jonaheinke/dac/spice/test/Draft1.asc

C1: cap; 3µ3
C2: cap; 22µ
C3: cap; 3µ3
C4: cap; 220µ
Q1: pnp
Q2: npn
Q3: pnp
Q4: pnp
Q5: npn
Q6: npn
Q7: npn
R1: res; 2k2
R2: res; 10k
R3: res; 10k
R4: res; 22k
R5: res; 22k
R6: res; 100
R7: res; 9k
R8: res; 1k
R9: res; 100k
R10: res; 5R6
R11: res; 10k
R12: res; 250
V1: voltage; SINE(0 250m 1k)
V2: voltage; 11; Rser=100k
V3: voltage; 22
Named nets: 0
