jonaheinke/dac/spice/test/Example_BJT_THD_TEST.asc

C1: cap; 1µ
C2: cap; 330µ
J1: njf; BF862
M2: nmos; ZVN4306A
R1: res; 100k
R2: res; 47k
R3: res; 68
R4: res; 470
R5: res; 68
R6: res; 2k
R7: res; 250
R8: res; 68
V1: voltage; 22
V2: voltage; SINE(0 250m 1k)
Named nets: 0, out
;.inc Analyzer_Controls.txt
;.tran 0 {AnalysisTime} {SettlingTime} {MaxTimestep}
.inc BF862.sub
.inc ZVN4306.sub
.tran 0 100m 0 1u
.four 1k V(out)
.option numdgt=7
;.inc ZXMN10A08E6.sub
;.inc 2SK209GR.txt
.model 2SK209BL NJF vto = -0.7869
+ beta = 0.021 lambda = 6.15e-3 rd = 12.194
+ rs = 16.746 is = 2.613e-15 cgd = 1.458e-11
+ cgs = 1.478e-11 pb = 0.3754
+ fc = 0.5 N = 1
;.op
.options plotwinsize=0
