jonaheinke/dac/spice/current_source.asc

Q1: pnp; 2N4126
Q2: pnp; 2N4126
R1: res; 150
R2: res; 33k
R3: res; 800
V2: voltage; SINE(20 1 20k); Rser=10
Named nets: 0, input, output
;.step dec param R 1 100k 100
;.op
;.tran 0 30 0 0.1
;.step param V 1 12 1
.tran 0 0.5m 0 10n
