jonaheinke/dac/spice/DC_detection_2.asc

C1: cap; 10µ
C2: cap; 10µ
C3: cap; 2µ2
D1: diode; 1N914
D2: diode; 1N914
D3: diode; 1N914
D4: diode; 1N914
Q2: pnp
Q3: pnp
Q4: npn
Q5: npn
R1: res; 100k
R2: res; 100k
R3: res; 10k
R4: res; 100k
R5: res; 100k
R6: res; 2k5
R7: res; 22k
R8: res; 22k
R9: res; 47k
R10: res; 2k2
R11: res; 100k
R12: res; 100k
V1: voltage; 24; Rser=2
V3: voltage; SINE(0 10 2); Rser=1
V4: voltage; PULSE(2.1 2.5 0 120m 1 1)
V5: voltage; PULSE(0 5 1 100m 100m 100 102 1); Rser=1
Named nets: 0
.tran 0 8s 0 100u
;step param offset 2 2.5 0.1
