jonaheinke/dac/spice/DC_detection_3.asc

C1: cap; 10µ
C2: cap; 10µ
C3: cap; 3µ3
C4: cap; 10µ
D1: diode; 1N914
D2: diode; 1N914
Q1: npn
Q2: pnp
Q3: npn
Q4: npn
R1: res; 100k
R2: res; 100k
R3: res; 10k
R4: res; 100k
R5: res; 2k8
R6: res; 22k
R7: res; 430k
R8: res; 2k8
R9: res; 100k
U2: UniversalOpAmp
V1: voltage; PULSE(0 24 500m 50m 10 20 10); Rser=2
V2: voltage; SINE(0 5 10); Rser=1
V3: voltage; PULSE(2.1 2.5 0 120m 1 1)
V4: voltage; PULSE(0 10 1 100m 100m 100 102 1); Rser=1
V5: voltage; 24; Rser=2
V6: voltage; 2.5
V7: voltage; PULSE(0 21 500m 100m 100m 10 10); Rser=2
Named nets: 0
.tran 0 8s 0 100u
;step param offset 2 2.5 0.1
