jonaheinke/dac/spice/Draft3.asc

C1: cap; 22µ
D1: LED
D2: diode
D3: diode
D4: LED
Q1: npn
Q2: npn
R1: res; 8k2
R2: res; 47k
R4: res; 1k
R5: res; 100k
R6: res; 1k
R7: res; 2k2
U3: UniversalOpAmp
U4: UniversalOpAmp
V1: voltage; PULSE(0 3V3 100m 10m 10m 1.5 3 1)
V2: voltage; 12
V3: voltage; 24
V4: voltage; 3V3
Named nets: 0
.tran 0 4 0 10m
