jonaheinke/dac/spice/Draft4.asc

C1: cap; 10µ
C2: cap; 470µ
C3: cap; 10µ
J1: pjf; 2N5460
Q1: pnp
R1: res; 1
R2: res; 10
R3: res; 100
R5: res; 5k1
R6: res; 100k
V1: voltage; PULSE(0 24 100m 10m 10m 100)
V2: voltage; 8
Named nets: 0
.tran 0 1 0 100u
