jonaheinke/dac/spice/Draft5.asc

C1: cap; 100n
C2: cap; 1n
C3: cap; 470µ
L1: ind; 250µ
R1: res; 15
R2: res; 32
R3: res; 15
V1: voltage; ""; AC 1; Rser=1
Named nets: 0
.ac dec 10 10 100k
