jonaheinke/dac/spice/full_amplifier.asc

C1: cap; 30p
C2: cap; 470µ; Rser=100m Lser=20n
C3: cap; 470µ; Rser=100m Lser=20n
C4: cap; 3µ3
C5: cap; 10µ
C6: cap; 2m2; Rser=100m Lser=20n
C8: cap; 2m2; Rser=100m Lser=20n
C9: cap; 10µ
C10: cap; 100n
C11: cap; 100n
C12: cap; 100n
C13: cap; 100n
C15: cap; 10µ
C16: cap; 10µ
C17: cap; 10µ
C18: cap; 10µ
D1: diode
D2: diode
D3: diode
D4: diode
L1: ind2; 1.3; Rser=100
L2: ind2; 8m; Rser=0.6
L3: ind2; 8m; Rser=0.6
Q1: pnp; 2N2907
Q2: pnp; 2N2907
Q3: pnp; 2N2907
Q4: pnp; 2N2907
Q5: npn
Q6: npn
Q7: npn
Q8: npn
Q9: pnp
Q10: pnp; 2SAR583D3
Q11: npn; 2SCR583D3
Q12: npn
Q13: npn
Q14: pnp
Q15: pnp
Q16: npn; BC547B
Q17: npn; BC547B
Q18: pnp
Q19: pnp
R1: res; 680
R2: res; 27k
R3: res; 470
R4: res; 470
R5: res; 430
R6: res; 430
R7: res; 2k2
R8: res; 2
R9: res; 2
R10: res; 100
R11: res; 100
R12: res; 2k2
R13: res; 20k
R14: res; 1k2
R15: res; 2k2
R16: res; 68
R17: res; 27k
R18: res; 20k
R19: res; 250
R20: res; 22
R21: res; 12
R22: res; 10k
R23: res; 10k
R24: res; 10k
R25: res; 10k
R30: res; 10k
R31: res; 10k
V1: voltage; 0
V2: voltage; SINE(0 325 50 0); AC 325; Rser=2
V3: voltage; 25
V4: voltage; 25
V5: voltage; SINE(0 0.5 20k)
Named nets: 0, output, bias+, bias-, preVAS, fb, base, in
;ac dec 100 100 1MEG
;tran 80u
.tran 0 3.01 3 100u
.option plotwinsize=0
;maxstep=0.48831106u
.four 20kHz 5 2 v(output)
;maxstep=0.12207776u
K1 L1 L2 L3 1
