jonaheinke/dac/spice/new_amplifier.asc

C1: cap; 3µ3
C2: cap; 22µ
C3: cap; 3µ3
C4: cap; 220µ
C5: cap; 10µ
C6: cap; 10µ
C7: cap; 3µ3
C8: cap; 220µ
C9: cap; 3µ3
C10: cap; 220µ
M2: nmos; ZVN4306A
Q1: pnp
Q2: npn
Q3: pnp
Q4: pnp
Q5: npn
Q6: npn
Q7: npn
Q8: npn
Q9: npn
Q10: npn
R1: res; 3k3
R2: res; 3k3
R3: res; 3k3
R4: res; 22k
R5: res; 22k
R6: res; 100
R7: res; 5k
R8: res; 5k
R9: res; 12k
R10: res; 5R6
R11: res; 10k
R12: res; 250
R13: res; 100k
R14: res; 22k
R15: res; 100k
R16: res; 100k
R17: res; 10k
R18: res; 10
R19: res; 47
R20: res; 5R6
R21: res; 10
R22: res; 250
R23: res; 68
R24: res; 10k
R25: res; 250
R26: res; 200
R27: res; 5k
R28: res; 5k
V1: voltage; SINE(0 500m 1k)
V2: voltage; 12; Rser=100k
V3: voltage; 22; Rser=0
V4: voltage; 22; Rser=0
Named nets: 0, out
.tran 0 40m 10m 1u
.four 1k V(out)
.option plotwinsize=0
.option numdgt=7
.inc ZVN4306.sub
