jonaheinke/dac/spice/output_circuit.asc

C1: cap; 100n
C2: cap; 470µ
C3: cap; 3µ3
R1: res; 15
R2: res; 15
R3: res; 22k
R4: res; 15
R5: res; 50m
R6: res; 32
V1: voltage; ""; AC 1
Named nets: 0
.ac oct 12 10 25k
