jonaheinke/dac/spice/power_supply.asc

C1: cap; 470µ; Rser=100m Lser=20n
C2: cap; 2m2; Rser=100m Lser=20n
C3: cap; 100µ; Rser=30m
C5: cap; 10µ
C6: cap; 100n
C7: cap; 100n
C8: cap; 100n
C9: cap; 100n
C10: cap; 10µ
C11: cap; 10µ
C12: cap; 470µ
C13: cap; 10µ
D1: diode
D2: diode
D3: diode
D4: diode
I1: current; PULSE(10m 300m 0 100u 100u 300u 3m)
I2: current; 300m
L1: ind2; 1.7; Rser=100
L2: ind2; 7m; Rser=0.6
L3: ind2; 7m; Rser=0.6
M1: pmos; FDC5614P
Q1: npn; BC547B
Q2: npn; BC547B
R1: res; 100k
R2: res; 10k
R3: res; 10k
R4: res; 11k
R5: res; 0R58
R6: res; 10k
R7: res; 20
R8: res; 10k
R9: res; 1
R10: res; 1m
V1: voltage; SINE(0 325 50 0); AC 325; Rser=2
Named nets: 0
K1 L1 L2 L3 1
.tran 0 2 0 100u
