jonaheinke/dac/spice/self_vas.asc

C1: cap; 13µ3
C2: cap; 10µ
C5: cap; 3µ3
C6: cap; 470µ
C7: cap; 10µ
D1: diode; 1N4148
D2: diode; 1N4148
Q1: npn
Q2: npn; 2N2222
Q3: npn; 2N2222
Q4: npn
Q5: npn; 2N2222
Q6: npn
Q7: npn
Q8: npn; 2N2222
Q9: pnp
Q10: pnp
R1: res; 5k1
R2: res; 10k
R3: res; 1m
R4: res; 5k1
R5: res; 6R7
R6: res; 100
R7: res; 22k
R8: res; 2k2
R9: res; 22k
R10: res; 2k2
R11: res; 100k
R12: res; 15
R13: res; 22k
R14: res; 22k
R15: res; 47k
R16: res; 250
R17: res; 10k
V1: voltage; SINE(0 500m 1k)
V2: voltage; 22
V3: voltage; ""; AC 1
Named nets: 0, out
.tran 0 40m 10m 100n
.four 1k V(out)
.option plotwinsize=0
;.ac oct 8 10 20k
