jonaheinke/dac/spice/self_vas_2.asc

C1: cap; 4µ7
C2: cap; 10µ
C4: cap; 470µ
Q1: npn; 2N2222
Q4: npn
Q5: npn
Q6: npn
Q7: npn
Q9: pnp
Q10: pnp
R1: res; 4k3
R2: res; 10k
R3: res; 1k
R4: res; 4k3
R5: res; 42
R7: res; 22k
R8: res; 8R2
R9: res; 2k2
R11: res; 15
R14: res; 22k
R15: res; 9k
R16: res; 1k5
R17: res; 22k
V1: voltage; SINE(0 1.5 1k)
V2: voltage; 22
V3: voltage; ""; AC 1
Named nets: 0, out
.tran 0 40m 10m 100n
.four 1k V(out)
.option plotwinsize=0
;.ac oct 8 5 1MEG
