jonaheinke/dac/spice/opamp_amplifier.asc

C1: cap; 10µ
Q1: pnp
Q2: pnp
Q3: npn
Q4: npn
Q5: npn
Q6: pnp
Q7: pnp
R1: res; 20k
R2: res; 2k2
R3: res; 20k
R4: res; 150
R5: res; 24
R6: res; 2k2
R7: res; 900
R8: res; 2
R9: res; 2
R10: res; 24
R11: res; 24
R12: res; 4k7
U1: OP413
V1: voltage; 15; Rser=1
V2: voltage; 15; Rser=1
V3: voltage; 0; AC 1
Named nets: 0
.tran 0 1 0 100u
