jonaheinke/dac/spice/opamp_amplifier_self.asc

C2: cap; 100p
D1: diode; 1N4148
D2: diode; 1N4148
Q1: pnp
Q2: npn
Q3: npn
Q4: pnp
Q5: npn; 2N2222
Q6: pnp; 2N2907
R1: res; 33
R3: res; 22k
R4: res; 22k
R5: res; 120
R6: res; 32
R8: res; 2
R9: res; 2
R10: res; 33
R11: res; 120
U1: OP27
V1: voltage; SINE(15 50m 40k); Rser=1
V2: voltage; 15; Rser=1
V3: voltage; SINE(0 8 20k)
Named nets: 0, OUT
.tran 0 800u 0 0.1u
.four 20k 10 V(OUT)
.option plotwinsize=0
