jonaheinke/dac/spice/capacitance_multiplier.asc

C1: cap; 47µ
C2: cap; 470µ
I1: current; PULSE(10m 100m 0 100u 100u 300u 3m)
Q1: npn
Q2: pnp
R1: res; 3k3
V1: voltage; PULSE(0 30 10m 2m 0 1 0 1)
V2: voltage; SINE(23 2 100)
Named nets: 0
.tran 0 100m 0 100u
