jonaheinke/dac/spice/current_clamp.asc

D1: schottky; DFLS220L
D2: schottky; DFLS220L
M1: pmos; HAT1023R
M2: nmos; AP9465GEM
Q1: npn; FZT849
Q2: pnp
Q12: pnp; 2N2907
Q13: npn
R1: res; 1
R2: res; 20
R3: res; 33k
R4: res; 33k
R5: res; 1m
R22: res; 0.67
R23: res; 33k
R24: res; 33k
R25: res; 10
V1: voltage; PULSE(0 40 0 1 0 0 0 1); Rser=1
V2: voltage; 10; Rser=5
V3: voltage; PULSE(0 30 0 1 0 0 0 1); Rser=1
V4: voltage; -10; Rser=5
Named nets: 0
.tran 0 1 0 1m
