jonaheinke/dac/spice/DC_detection.asc

C1: cap; 10µ
C2: cap; 10µ
C3: cap; 10µ
C4: cap; 10µ
D1: schottky; BAT54
D2: schottky; BAT54
D3: schottky; BAT54
D4: schottky; BAT54
D5: schottky; BAT54
D6: schottky; BAT54
D7: diode
Q1: npn
Q2: pnp
Q3: pnp
Q4: pnp; 2SAR544P
Q5: npn
R1: res; 100k
R2: res; 100k
R3: res; 22k
R4: res; 100k
R5: res; 10k
R6: res; 2k5
R7: res; 620
R8: res; 1k
R9: res; 100k
R10: res; 100k
R11: res; 1k
R12: res; 22k
R13: res; 100k
V1: voltage; 30; Rser=3
V2: voltage; PULSE(30 0 0 100m 1); Rser=3
V3: voltage; SINE(5 5 50)
V4: voltage; PULSE(2.1 2.5 0 120m 1 1)
V5: voltage; PULSE(0 340 0 6m 6m 3m 20m 50)
Named nets: 0
.tran 0 10s 0 100u
;step param offset 2 2.5 0.1
