jonaheinke/dac/spice/Draft2.asc

C1: cap; 1µ
C2: cap; 22n
C3: cap; 100µ
R1: res; 16
R2: res; 330
R3: res; 16
V1: voltage; ""; AC 1; Rser=6
Named nets: 0, output
.ac dec 101 1 20k
