jonaheinke/dac/spice/input.asc

C2: cap; 120p
C3: cap; 2µ2
Q1: pnp
R1: res; {Rtop}
R2: res; {Rbottom}
R3: res; 68
R5: res; 22k
R6: res; 600
Vin: voltage; ""; AC 1
Named nets: 0, input
.step param Rbottom 1k 10k 1k
.param Rtop=10k+1m-Rbottom
.ac dec 101 1 1MEG
