jonaheinke/dac/spice/loudness_control_2.asc

C1: cap; 2µ2
C3: cap; 1µ
R1: res; 40k
R2: res; {Rbottom}
R3: res; {Rtop}
R4: res; 20k
R7: res; 750
V1: voltage; ""; AC 1
Named nets: 0
.step param Rbottom 1k 12k 1k
.ac oct 10 5 24k
.param Rtop=12k+1m-Rbottom
