jonaheinke/dac/spice/Draft1.asc

C2: cap; 50µ
C3: cap; 50µ
D1: diode
D2: diode
I1: current; 24m; load
Q1: npn
R2: res; 670
R3: res; 32k
R4: res; 20
V1: voltage; PULSE(36 40 0 3.5m 3.5m 3m 10m 10); AC 2
V2: voltage; SINE(36 5 20k); AC 5
Named nets: 0
;tran 0 100m 0 1u
.ac oct 10 1 24k
