jonaheinke/dac/spice/loudness_control.asc

C1: cap; 22µ
C2: cap; 220n
R1: res; 1m
R2: res; {Rbottom}
R3: res; {Rtop}
R4: res; 100
R5: res; 2k
R6: res; 6k
V1: voltage; ""; AC 10
Named nets: 0
.step param Rbottom 1m 10k 1k
.step param Rtop 10k 1m -1k
.ac oct 10 10 20k
