jonaheinke/dac/spice/kicad_spice_project/kicad_spice_project.kicad_sch

## KiCad design spice/kicad_spice_project/kicad_spice_project.kicad_sch (2023-07-18)

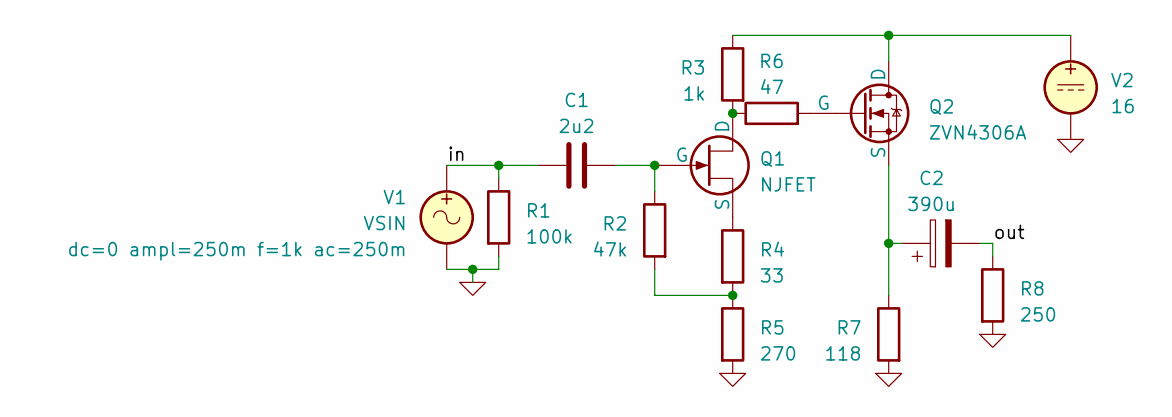
[picture p16: schematic kicad_spice_project.kicad_sch]

Parts:
C1: 2u2
C2: 390u
Q1: NJFET
Q2: ZVN4306A
R1: 100k
R2: 47k
R3: 1k
R4: 33
R5: 270
R6: 47
R7: 118
R8: 250
V1: VSIN
V2: 16

Connections:
0: R1.2, R5.2, R7.2, R8.2, V1.2, V2.2
unnamed: C1.2, Q1.2 (G), R2.1
unnamed: C2.1, Q2.3 (S), R7.1
unnamed: Q1.1 (D), R3.2, R6.1
unnamed: Q1.3 (S), R4.1
unnamed: Q2.1 (D), R3.1, V2.1
unnamed: Q2.2 (G), R6.2
unnamed: R2.2, R4.2, R5.1
in: C1.1, R1.1, V1.1
out: C2.2, R8.1
